night-ghost/JAFaR/docs/arduino_files.jpg

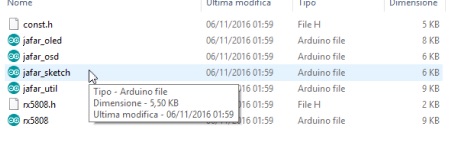
docs/arduino_files.jpg
