night-ghost/JAFaR/docs/board_e_porta.jpg

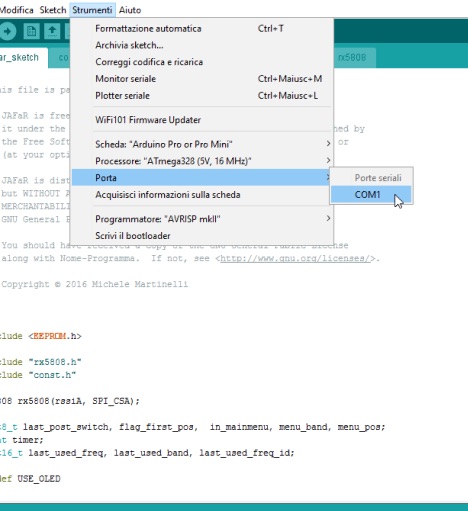
docs/board_e_porta.jpg
