night-ghost/JAFaR/docs/carica.jpg

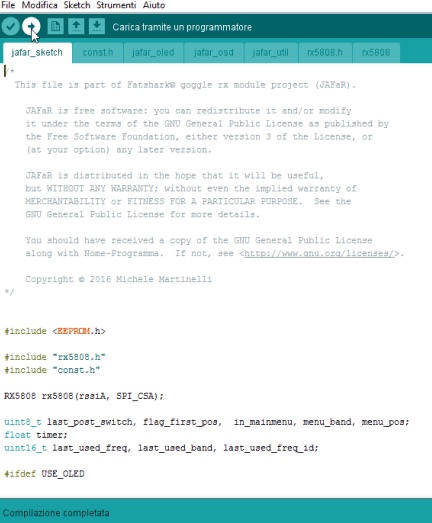
docs/carica.jpg
