night-ghost/JAFaR/docs/modules_version.jpg

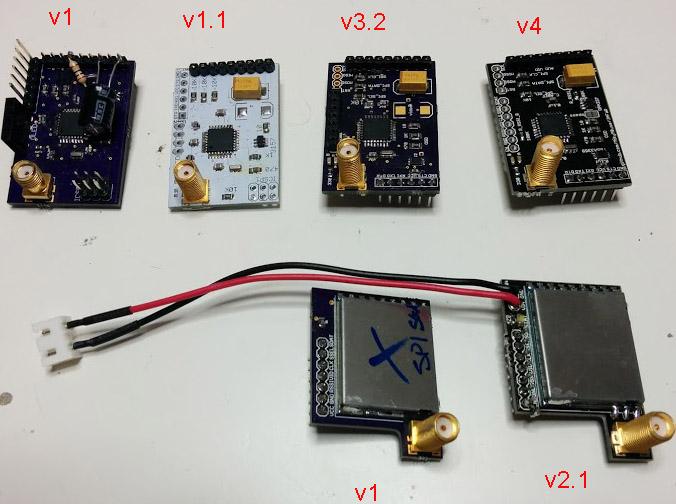
docs/modules_version.jpg
