night-ghost/JAFaR/docs/installa_libs.jpg

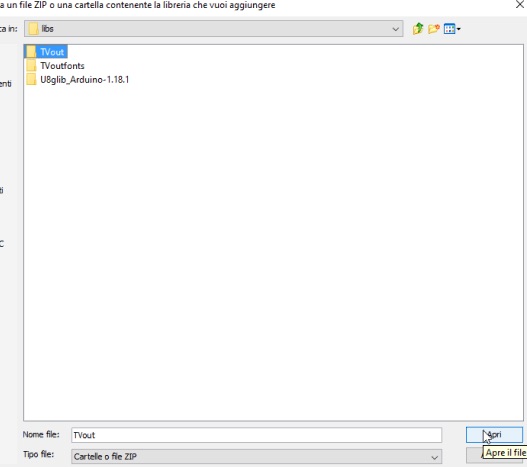
docs/installa_libs.jpg
