night-ghost/JAFaR/docs/installa_zip.png

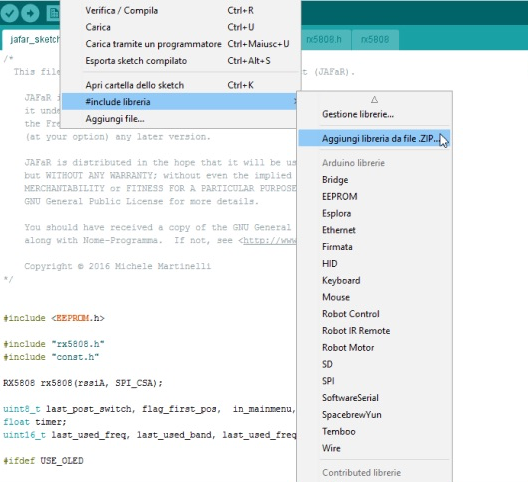
docs/installa_zip.png
