night-ghost/JAFaR/jafar_sketch/text.h

unsigned char band_a_bits[] U8G_PROGMEM = {
  0x00, 0x00, 0x00, 0x00,
  0x00, 0x00, 0x00, 0x00,
  0x00, 0x00, 0x00, 0x00,
  0x00, 0x80, 0x03, 0x00,
  0x00, 0x80, 0x03, 0x00,
  0x00, 0xc0, 0x03, 0x00,
  0x00, 0xc0, 0x07, 0x00,
  0x00, 0xe0, 0x07, 0x00,
  0x00, 0xe0, 0x0f, 0x00,
  0x00, 0xe0, 0x0f, 0x00,
  0x00, 0xf0, 0x0f, 0x00,
  0x00, 0xf0, 0x1f, 0x00,
  0x00, 0xf0, 0x1e, 0x00,
  0x00, 0xf8, 0x3e, 0x00,
  0x00, 0x78, 0x3c, 0x00,
  0x00, 0x7c, 0x3c, 0x00,
  0x00, 0x7c, 0x7c, 0x00,
  0x00, 0x3c, 0x7c, 0x00,
  0x00, 0x3e, 0xf8, 0x00,
  0x00, 0x3e, 0xf8, 0x00,
  0x00, 0xff, 0xff, 0x00,
  0x00, 0xff, 0xff, 0x01,
  0x00, 0xff, 0xff, 0x01,
  0x80, 0xff, 0xff, 0x03,
  0x80, 0x0f, 0xe0, 0x03,
  0xc0, 0x07, 0xe0, 0x03,
  0xc0, 0x07, 0xc0, 0x07,
  0xc0, 0x07, 0xc0, 0x07,
  0xe0, 0x03, 0xc0, 0x0f,
  0x00, 0x00, 0x00, 0x00,
  0x00, 0x00, 0x00, 0x00,
  0x00, 0x00, 0x00, 0x00,
};

unsigned char band_b_bits[] U8G_PROGMEM = {
  0x00, 0x00, 0x00, 0x00,
  0x00, 0x00, 0x00, 0x00,
  0x00, 0x00, 0x00, 0x00,
  0x00, 0xff, 0x07, 0x00,
  0x00, 0xff, 0x1f, 0x00,
  0x00, 0xff, 0x3f, 0x00,
  0x00, 0xff, 0x7f, 0x00,
  0x00, 0x0f, 0x7c, 0x00,
  0x00, 0x0f, 0x7c, 0x00,
  0x00, 0x0f, 0x78, 0x00,
  0x00, 0x0f, 0x78, 0x00,
  0x00, 0x0f, 0x7c, 0x00,
  0x00, 0x0f, 0x7e, 0x00,
  0x00, 0xff, 0x3f, 0x00,
  0x00, 0xff, 0x1f, 0x00,
  0x00, 0xff, 0x3f, 0x00,
  0x00, 0xff, 0x7f, 0x00,
  0x00, 0x0f, 0xf8, 0x00,
  0x00, 0x0f, 0xf0, 0x01,
  0x00, 0x0f, 0xf0, 0x01,
  0x00, 0x0f, 0xf0, 0x01,
  0x00, 0x0f, 0xf0, 0x01,
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
  0x00, 0xf0, 0x01, 0x00,
  0x00, 0xf0, 0x01, 0x00,
  0x00, 0xf8, 0x01, 0x00,
  0x00, 0xf8, 0x00, 0x00,
  0x00, 0xf8, 0x00, 0x00,
  0x00, 0x7c, 0x00, 0x00,
  0x00, 0x7c, 0x00, 0x00,
  0x00, 0x7c, 0x00, 0x00,
  0x00, 0x00, 0x00, 0x00,
  0x00, 0x00, 0x00, 0x00,
  0x00, 0x00, 0x00, 0x00,
};

unsigned char chan_8_bits[] U8G_PROGMEM = {
  0x00, 0x00, 0x00, 0x00,
  0x00, 0x00, 0x00, 0x00,
  0x00, 0x00, 0x00, 0x00,
  0x00, 0xf0, 0x07, 0x00,
  0x00, 0xfc, 0x1f, 0x00,
  0x00, 0xfe, 0x3f, 0x00,
  0x00, 0xfe, 0x3f, 0x00,
  0x00, 0x1f, 0x7e, 0x00,
  0x00, 0x1f, 0x7c, 0x00,
  0x00, 0x1f, 0x7c, 0x00,
  0x00, 0x1f, 0x7c, 0x00,
  0x00, 0x3f, 0x3e, 0x00,
  0x00, 0x7e, 0x3f, 0x00,
  0x00, 0xfc, 0x1f, 0x00,
  0x00, 0xf8, 0x0f, 0x00,
  0x00, 0xf8, 0x0f, 0x00,
  0x00, 0xfc, 0x1f, 0x00,
  0x00, 0x3f, 0x3f, 0x00,
  0x00, 0x1f, 0x7e, 0x00,
  0x80, 0x0f, 0x7c, 0x00,
  0x80, 0x0f, 0xf8, 0x00,
  0x80, 0x0f, 0xf8, 0x00,
  0x80, 0x0f, 0xf8, 0x00,
  0x80, 0x0f, 0xf8, 0x00,
  0x80, 0x1f, 0xfc, 0x00,
  0x00, 0xff, 0x7f, 0x00,
  0x00, 0xfe, 0x3f, 0x00,
  0x00, 0xfe, 0x1f, 0x00,
  0x00, 0xf8, 0x0f, 0x00,
  0x00, 0x00, 0x00, 0x00,
  0x00, 0x00, 0x00, 0x00,
  0x00, 0x00, 0x00, 0x00,
};
