night-ghost/JAFaR/jafar_sketch/rx5808.cpp

/*
This file is part of Fatshark© goggle rx module project (JAFaR).

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
    Copyright © 2016 Michele Martinelli
  */

//#include <Wire.h>
//#include <EEPROM.h>
#include "rx5808.h"
#define RSSI_THRESH (scanVec[getMaxPos()]-5) //strong channels are near to the global max



uint16_t rssi_min = 1024;
uint16_t rssi_max = 0;

RX5808::RX5808(uint16_t RSSIpin, uint16_t CSpin) {
  _rssiPin = RSSIpin;
  _csPin = CSpin;
  _stop_scan = 0;
}

uint8_t RX5808::getfrom_top8(uint8_t index) {
  return scanVecTop8[index];
}

uint8_t* RX5808::getTop8() {
  return scanVecTop8;
}

void RX5808::compute_top8(void) {
  uint16_t scanVecTmp[CHANNEL_MAX];
  uint8_t _chan;

  memcpy(scanVecTmp, scanVec, sizeof(uint16_t)*CHANNEL_MAX);

  for (int8_t i = 7; i >= 0; i--) {
    uint16_t maxVal = 0;
    uint8_t maxPos = 0;
    for (_chan = CHANNEL_MIN; _chan < CHANNEL_MAX; _chan++) {
      if (maxVal < scanVecTmp[_chan]) { //new max
        maxPos = _chan;
        maxVal = scanVecTmp[_chan];
      }
    }

    //maxPos is the maximum
    scanVecTop8[i] = maxPos;
    scanVecTmp[maxPos] = 0;
  }
}

uint16_t RX5808::getRssi(uint16_t channel) {
  return scanVec[channel];
}

//stop scan
void RX5808::abortScan(void) {
  _stop_scan = 1;
}

//get the rssi value of a certain channel of a band and map it to 1...norm
uint16_t RX5808::getVal(uint8_t band, uint8_t channel, uint8_t norm) {
  return map(scanVec[8 * band + channel], 1, BIN_H, 1, norm);
}

//get the rssi value of a certain channel and map it to 1...norm
uint16_t RX5808::getVal(uint8_t pos, uint8_t norm) {
  return map(scanVec[pos], 1, BIN_H, 1, norm);
}

//get the maximum rssi value for a certain band and map it to 1...norm
uint16_t RX5808::getMaxValBand(uint8_t band, uint8_t norm) {
  int16_t _chan;
  uint16_t maxVal = 0;
  for (_chan = 8 * band; _chan < 8 * band + 8; _chan++) {
    if (maxVal < scanVec[_chan]) { //new max
      maxVal = scanVec[_chan];
    }
  }
  return map(maxVal, 1, BIN_H, 1, norm);
}

//get the channel with max rssi value for a certain band
uint16_t RX5808::getMaxPosBand(uint8_t band) {
  int16_t _chan;
  uint16_t maxVal = 0, maxPos = 8 * band;
  for (_chan = 8 * band; _chan < 8 * band + 8; _chan++) {
    if (maxVal < scanVec[_chan]) { //new max
      maxPos = _chan;
      maxVal = scanVec[_chan];
    }
  }
  return maxPos;
}

//get the minimum rssi value for a certain band
uint16_t RX5808::getMinPosBand(uint8_t band) {
  int16_t _chan;
  uint16_t minVal = 1000, minPos = 8 * band;
  for (_chan = 8 * band; _chan < 8 * band + 8; _chan++) {
    if (minVal > scanVec[_chan]) { //new max
      minPos = _chan;
      minVal = scanVec[_chan];
    }
  }
  return minPos;
}

//get global max
uint16_t RX5808::getMaxPos() {
  uint8_t _chan;
  uint16_t maxVal = 0, maxPos = 0;
  for (_chan = CHANNEL_MIN; _chan < CHANNEL_MAX; _chan++) {
    if (maxVal < scanVec[_chan]) { //new max
      maxPos = _chan;
      maxVal = scanVec[_chan];
    }
  }
  return maxPos;
}

//get global min
uint16_t RX5808::getMinPos() {
  uint8_t _chan;
  uint16_t minVal = 1000, minPos = 0;
  for (_chan = CHANNEL_MIN; _chan < CHANNEL_MAX; _chan++) {
    if (minVal > scanVec[_chan]) { //new max
      minPos = _chan;
      minVal = scanVec[_chan];
    }
  }
  return minPos;
}

uint16_t RX5808::getCurrentRSSI(uint16_t norm_min, uint16_t norm_max) {
  uint16_t rssi =  _readRSSI();
  rssi = constrain(rssi, rssi_min, rssi_max);
  rssi = map(rssi, rssi_min, rssi_max, norm_min, norm_max);   // scale from 1..100%
  return rssi;
}

uint16_t RX5808::getCurrentRSSI() {
  return _readRSSI();
}

void RX5808::init() {
  pinMode (_csPin, OUTPUT);
  pinMode (_rssiPin, INPUT);

  /*
   * Hardware SPI
   * - SPI Enable
   * - LSB first
   * - Master mode
   * - Leading edge rising, Leading edge sample
   * - SCK = 0 = fosc/4 i.e. 4Mhz
   */
  SPCR=(1<<SPE)|(1<<DORD)|(1<<MSTR);

  rssi_min = eeprom_read_word(EEPROM_ADR_RSSI_MIN_L);
  rssi_max = eeprom_read_word(EEPROM_ADR_RSSI_MAX_L);

  /*
    digitalWrite(_csPin, LOW);
    SPI.transfer(0x10);
    SPI.transfer(0x01);
    SPI.transfer(0x00);
    SPI.transfer(0x00);
    digitalWrite(_csPin, HIGH);
  */
  if (abs(rssi_max - rssi_min > 300) || abs(rssi_max - rssi_min < 50))
    calibration();

  scan(1, BIN_H);
}

//do a complete scan and normalize all the values
void RX5808::scan(uint16_t norm_min, uint16_t norm_max) {

  for (uint16_t _chan = CHANNEL_MIN; _chan < CHANNEL_MAX; _chan++) {
    if (_stop_scan) {
      _stop_scan = 0;
      return;
    }

    uint32_t freq = pgm_read_word_near(channelFreqTable + _chan);
    setFreq(freq);
    _wait_rssi();

    uint16_t rssi =  _readRSSI();
#ifdef RXDEBUG
    Serial.print(_chan, DEC);
    Serial.print("\t");
    Serial.print(freq, DEC);
    Serial.print("\t");
    Serial.println(rssi, DEC);
    _delay(500);
#endif

    rssi = constrain(rssi, rssi_min, rssi_max);
    rssi = map(rssi, rssi_min, rssi_max, norm_min, norm_max);   // scale from 1..100%
    scanVec[_chan] = rssi;
  }
}

void RX5808::updateRssi(uint16_t norm_min, uint16_t norm_max, uint16_t channel) {
  uint16_t rssi =  _readRSSI();
  rssi = constrain(rssi, rssi_min, rssi_max);
  rssi = map(rssi, rssi_min, rssi_max, norm_min, norm_max);   // scale from 1..100%
  scanVec[channel] = rssi;
}

//same as scan, but raw values, used for calibration
void RX5808::_calibrationScan() {
  for (uint16_t _chan = CHANNEL_MIN; _chan < CHANNEL_MAX; _chan++) {

    uint32_t freq = pgm_read_word_near(channelFreqTable + _chan);
    setFreq(freq);
    _wait_rssi();
    scanVec[_chan] = _readRSSI();
  }
}

void RX5808::_wait_rssi() {
  // 30ms will to do a 32 channels scan in 1 second
#define MIN_TUNE_TIME 30
  _delay(MIN_TUNE_TIME);
}

//simple avg of 4 value
uint16_t RX5808::_readRSSI() {
  volatile uint32_t sum = 0;
  _delay(9);
  sum = analogRead(_rssiPin);
  sum += analogRead(_rssiPin);
  _delay(1);
  sum += analogRead(_rssiPin);
  sum += analogRead(_rssiPin);
  return sum / 4.0;
}

//compute the min and max RSSI value and store the values in EEPROM
void RX5808::calibration() {
  int i = 0, j = 0;
  uint16_t  rssi_setup_min = 1024, minValue = 1024;
  uint16_t  rssi_setup_max = 0, maxValue = 0;

  for (j = 0; j < 5; j++) {
    _calibrationScan();

    for (i = CHANNEL_MIN; i < CHANNEL_MAX; i++) {
      uint16_t rssi = scanVec[i];

      minValue = min(minValue, rssi);
      maxValue = max(maxValue, rssi);
    }

    rssi_setup_min = min(rssi_setup_min, minValue); //?minValue:rssi_setup_min;
    rssi_setup_max = max(rssi_setup_max, maxValue); //?maxValue:rssi_setup_max;
  }

  eeprom_write_word(EEPROM_ADR_RSSI_MIN_L, rssi_setup_min);
  eeprom_write_word(EEPROM_ADR_RSSI_MAX_L, rssi_setup_max);

  rssi_min = eeprom_read_word(EEPROM_ADR_RSSI_MIN_L);
  rssi_max = eeprom_read_word(EEPROM_ADR_RSSI_MAX_L);


  _delay(3000);

  return;
}

void RX5808::setFreq(uint32_t freq) {
  uint32_t _if = (freq - 479);

  uint32_t N = floor(_if / 64);
  uint32_t A = floor((_if / 2) % 32);
  uint32_t channelData = (N << 7) | (A & 0x7F);

#ifdef DEBUG
  Serial.print("N: ");
  Serial.println(N, DEC);

  Serial.print("A: ");
  Serial.println(A, DEC);

  Serial.print("setting ");
  Serial.println(channelData, HEX);
#endif

  serialEnable(HIGH);
  delayMicroseconds(1);
  serialEnable(LOW);

  sendCommand(8, 0, 0);

  serialEnable(HIGH);
  delayMicroseconds(1);
  serialEnable(LOW);

  sendCommand(1, 1, channelData);

  serialEnable(HIGH);
}

void RX5808::sendCommand(uint8_t addr, uint8_t readwrite, uint32_t data) {
  uint32_t spiData = (data << 5) | ((readwrite & 1) << 4) | (addr & 0xF);
  for(int i=0 ; i<4 ; i++) {
    SPDR = spiData & 0xFF;
    spiData >>= 8;
    while(!(SPSR & (1<<SPIF) ));
  }
}

void RX5808::serialEnable(const uint8_t _lev) {
  digitalWrite(_csPin, _lev);
}
